t0mg/wordclock/software/wordclock/src/src/Iot.h

#ifndef _IOT_H_
#define _IOT_H_

#include "Display.h"
#include "ClockFace.h"
#include "IotRangeValueParameter.h"

#include <MQTT.h>
#include <IotWebConf.h>
#include <IotWebConfESP32HTTPUpdateServer.h>
#include <RTClib.h>

// Maximum length of a single IoT configuration value.
#define IOT_CONFIG_VALUE_LENGTH 16

class Iot
{
public:
  Iot(Display *display, RTC_DS3231 *rtc);
  ~Iot();

  Iot(const Iot &) = delete;
  Iot &operator=(const Iot &) = delete;

  Iot(Iot &&) = delete;
  Iot &operator=(Iot &&) = delete;

  void setup();
  void loop();

  // Used for the C callback for the NTP sync.
  RTC_DS3231 *get_rtc() { return rtc_; }

private:
  // Clears the values of transient parameters.
  void clearTransientParams_();
  // Updates word clock's state to match the current configuration values.
  void updateClockFromParams_();
  // Updates the RTC based on current configuration
  void updateClockRTCFromParams_();
  // Checks for NTP setting and if enabled, attempts to update the RTC.
  void maybeSetRTCfromNTP_();
  // Sets the RTC from manual input
  void setRTCfromConfig_();
  // Connects to MQTT server.
  bool connectMQTT_();
  // Sends a 403 on the web server if the API is not enabled.
  bool checkAPIEnabledOr403_();
  // Toggles the display if payload is "ON" or "OFF".
  void toggleDisplay_(String payload);
  // Convenience method to format RgbColor for MQTT publication.
  static String rgbToMqttString_(RgbColor color)
  {
    return String(color.R) + "," + String(color.G) + "," + String(color.B);
  }
  // Convenience method to convert an MQTT payload into RgbColor.
  static bool mqttStringToRgb_(String payload, RgbColor *color);

  // Handles HTTP requests to web server's "/" path.
  void handleHttpToRoot_();
  // Handles form verification before saving.
  bool formValidator_(iotwebconf::WebRequestWrapper* webRequestWrapper);
  // Handles configuration changes.
  void handleConfigSaved_();
  // Handles wifi connexion success.
  void handleWifiConnection_();
  // Keep track of he first wifi connection callback.
  bool firstWifiConnection_ = true;
  // Connects to MQTT server using provided credentials.
  bool connectMqttOptions_();
  // Handles incoming MQTT messages.
  void mqttMessageReceived_(String &topic, String &payload);
  // Updates the display with an arbitrary payload.
  void setMatrixFromPayload_(String &payload);
  // Scrolls an arbirary text payload on the display.
  void scrollText_(String &text, RgbColor color, int speed, bool rightToLeft);

  // Whether IoT configuration was initialized.
  bool initialized_ = false;
  // Last MQTT connection attempt.;
  unsigned long last_mqtt_connection_attempt_ = 0;

  // Configuration portal's DNS server.
  DNSServer dns_server_;
  // Configuration portal's web server.
  WebServer web_server_;
  // Server for OTA firmware update.
  HTTPUpdateServer http_updater_;
  // MQTT client.
  MQTTClient mqtt_client_ = MQTTClient(256);
  // WiFi client (for MQTT).
  WiFiClient net_;

  // Word clock display.
  Display *display_ = nullptr;

  // RTC.
  RTC_DS3231 *rtc_ = nullptr;

  // Whether to reboot the ESP (after config updates if MQTT is enabled).
  bool needs_reboot_ = false;

  // Whether to attempt connecting to MQTT server.
  bool needs_mqtt_connect_ = false;

  // Timestamp of last MQTT push.
  unsigned long last_mqtt_report_ = 0;

  // MQTT topic prefix, derived from the clock name defined in the web UI.
  String mqtt_topic_prefix_;

  // Enables the boot animation.
  IotRangeValueParameter boot_animation_param_;
  // Value of the boot animation setting option.
  char boot_animation_enabled_value_[IOT_CONFIG_VALUE_LENGTH];
  
  // Clockface language selctor.
  iotwebconf::NumberParameter clockface_language_param_;
  // Value of the language parameter.
  char clockface_language_value_[IOT_CONFIG_VALUE_LENGTH];

  // Enable AM/PM display.
  IotRangeValueParameter show_ampm_param_;
  // Value of the AM/PM option.
  char show_ampm_value_[IOT_CONFIG_VALUE_LENGTH];

  // Sensitivity parameter for the LDR.
  IotRangeValueParameter ldr_sensitivity_param_;
  // Value of the LDR sensitivity parameter.
  char ldr_sensitivity_value_[IOT_CONFIG_VALUE_LENGTH];

  // Text color parameter.
  iotwebconf::TextParameter color_param_;
  // Value of the color parameter.
  char color_value_[IOT_CONFIG_VALUE_LENGTH];

  // Enables NTP time setting.
  IotRangeValueParameter ntp_enabled_param_;
  // Value of the NTP setting option.
  char ntp_enabled_value_[IOT_CONFIG_VALUE_LENGTH];

  // The timezone index from available options.
  iotwebconf::NumberParameter timezone_param_;
  // Index of the selected timezone.
  char timezone_value_[IOT_CONFIG_VALUE_LENGTH];

  // Manual time setting. Transient.
  iotwebconf::TextParameter manual_time_param_;
  // Time parameter value.
  char manual_time_value_[IOT_CONFIG_VALUE_LENGTH];

  // Enables API.
  IotRangeValueParameter api_enabled_param_;
  // Value of the API setting option.
  char api_enabled_value_[IOT_CONFIG_VALUE_LENGTH];

  // Enables MQTT client.
  IotRangeValueParameter mqtt_enabled_param_;
  // Value of the MQTT setting option.
  char mqtt_enabled_value_[IOT_CONFIG_VALUE_LENGTH];

  // MQTT server setting.
  iotwebconf::TextParameter mqtt_server_param_;
  // MQTT server value.
  char mqtt_server_value_[IOT_CONFIG_VALUE_LENGTH];

  // MQTT username setting.
  iotwebconf::TextParameter mqtt_user_param_;
  // MQTT username value.
  char mqtt_user_value_[IOT_CONFIG_VALUE_LENGTH];

  // MQTT password setting.
  iotwebconf::PasswordParameter mqtt_password_param_;
  // MQTT password value.
  char mqtt_password_value_[IOT_CONFIG_VALUE_LENGTH];

  // Config form groups.
  iotwebconf::ParameterGroup time_group_;
  iotwebconf::ParameterGroup display_group_;
  iotwebconf::ParameterGroup api_group_;
  iotwebconf::ParameterGroup mqtt_group_;

  // IotWebConf interface handle.
  IotWebConf iot_web_conf_;
};

#endif // _IOT_H_
